hominoids/SBC_Case_Builder/mod/case_rack.scad

/*
    This file is part of SBC Case Builder https://github.com/hominoids/SBC_Case_Builder
    Copyright 2025 Edward A. Kisiel hominoid@cablemi.com

    This program is free software: you can redistribute it and/or modify
    it under the terms of the GNU General Public License as published by
    the Free Software Foundation, either version 3 of the License, or
    (at your option) any later version.

    but WITHOUT ANY WARRANTY; without even the implied warranty of
    MERCHANTABILITY or FITNESS FOR A PARTICULAR PURPOSE.  See the
    GNU General Public License for more details.

    You should have received a copy of the GNU General Public License
    along with this program.  If not, see <http://www.gnu.org/licenses/>
    Code released under GPLv3: http://www.gnu.org/licenses/gpl.html

    case_rack(case_design,side)


           NAME: case_rack
    DESCRIPTION: creates 1u-2u rack cases
           TODO: none

          USAGE: case_rack(case_design,side)

*/

module case_rack(case_design,side) {

rack_asm_gap = .25;
rack_asm_size = 5;
rack_asm_hole = 2.25;

if(case_design == "rack" && side == "bottom") {
    difference() {
        union() {
            difference() {
                union() {
                    difference() {
                        translate([(width/2)-wallthick-gap,(depth/2)-wallthick-gap,(case_z-floorthick)/2]) 
                            cube_fillet_inside([width,depth,case_z-floorthick], 
                                vertical=[corner_fillet,corner_fillet,0,0], 
                                    top=[0,0,0,0], bottom=[edge_fillet,edge_fillet,edge_fillet,edge_fillet,edge_fillet], $fn=90);
                        translate([(width/2)-wallthick-gap,(depth/2)-wallthick-gap,floorthick+(floorthick+case_z)/2]) 
                            cube_fillet_inside([width-(wallthick*2),depth-(wallthick*2),case_z+floorthick], 
                                    vertical=[corner_fillet-wallthick,corner_fillet-wallthick,-wallthick,-wallthick],
                                        top=[0,0,0,0], bottom=[edge_fillet,edge_fillet,edge_fillet,edge_fillet,edge_fillet], $fn=90);
                        // case upper panel clamp holes
                        translate([150-gap-wallthick,-gap-adj,case_z-13+4]) 
                            panel_clamp("rear", "sloped", "m2", 6, 18, 5, [true,10,2,"default"]);
                        translate([150-gap-wallthick,depth-gap-(2*wallthick)+adj,
                            case_z-13+4]) panel_clamp("front", "sloped", "m2", 6, 18, 5, [true,10,2,"default"]);
                        if(rack_width == 19) { 
                            translate([300-gap-wallthick,-gap-adj,case_z-13+4]) 
                                panel_clamp("rear", "sloped", "m2", 6, 18, 5, [true,10,2,"default"]);
                            translate([300-gap-wallthick,depth-gap-(2*wallthick)+adj,
                                case_z-13+4]) panel_clamp("front", "sloped", "m2", 6, 18, 5, [true,10,2,"default"]);
                        }

                    }
                    // rack mounting tabs
                    translate([-gap-wallthick, -gap+(sidethick-wallthick), 0]) 
                        rack_end_bracket("left", rack_size, sidethick);
                    translate([width-wallthick-gap, -gap+(sidethick-wallthick), 0]) 
                        rack_end_bracket("right", rack_size, sidethick);

                    // bay divider walls
                    for(r = [0:len(rack_bay_sbc)-1]) {
                        if(rack_bay_wall[r] == true) {
                            translate([-gap-wallthick-1+rack_asm_gap/2+75*(r+1),-gap-wallthick-adj,0]) 
                                cube([2,depth,case_z-floorthick-2]);
                        }
                    }
                    // case upper panel clamps
                    translate([150-gap-wallthick,-gap-adj,case_z-13+4]) 
                        panel_clamp("rear", "sloped", "m2", 6, 18, 5, [false,10,2,"default"]);
                    translate([150-gap-wallthick,depth-gap-(2*wallthick)+adj,
                        case_z-13+4]) panel_clamp("front", "sloped", "m2", 6, 18, 5, [false,10,2,"default"]);
                    if(rack_width == 19) { 
                        translate([300-gap-wallthick,depth-gap-(2*wallthick)+adj,
                            case_z-13+4]) panel_clamp("front", "sloped", "m2", 6, 18, 5, [false,10,2,"default"]);
                        translate([300-gap-wallthick,-gap-adj,case_z-13+4]) 
                            panel_clamp("rear", "sloped", "m2", 6, 18, 5, [false,10,2,"default"]);
                    }

                    // case floor panel clamps
                    translate([150-gap-wallthick,(depth/2)-gap-wallthick,floorthick-adj-.5]) 
                        panel_clamp("bottom", "sloped", "m2", 6, 18, 5, [false,10,2,"default"]);
                    if(rack_width == 19) { 
                        translate([300-gap-wallthick,(depth/2)-gap-wallthick,floorthick-adj-.5]) 
                            panel_clamp("bottom", "sloped", "m2", 6, 18, 5, [false,10,2,"default"]);
                    }
                    // top support
                    translate([-gap,depth-gap-wallthick-18,case_z-floorthick]) rotate([0,0,270])
                        panel_clamp("rear", "sloped", "m2", 6, 18, 5, [false,10,2,"default"]);
                    translate([width-gap-(2*wallthick),depth-gap-wallthick-18,case_z-floorthick])  rotate([0,0,270])
                        panel_clamp("front", "sloped", "m2", 6, 18, 5, [false,10,2,"default"]);
    
                    translate([-gap,18-gap,case_z-floorthick]) rotate([0,0,270])
                        panel_clamp("rear", "sloped", "m2", 6, 18, 5, [false,10,2,"default"]);
                    translate([width-gap-(2*wallthick),18-gap,case_z-floorthick])  rotate([0,0,270])
                        panel_clamp("front", "sloped", "m2", 6, 18, 5, [false,10,2,"default"]);
    
                    // additive accessories
                    if(accessory_name != "none") {
                        for (i=[1:11:len(accessory_data[a[0]])-1]) {
                            class = accessory_data[a[0]][i];
                            type = accessory_data[a[0]][i+1];
                            loc_x = accessory_data[a[0]][i+2];
                            loc_y = accessory_data[a[0]][i+3];
                            loc_z = accessory_data[a[0]][i+4];
                            face = accessory_data[a[0]][i+5];
                            rotation = accessory_data[a[0]][i+6];
                            parametric = accessory_data[a[0]][i+7];
                            size = accessory_data[a[0]][i+8];
                            data = accessory_data[a[0]][i+9];
                            mask = accessory_data[a[0]][i+10];

                            if(class == "add1" && face == "bottom") {
                                parametric_move_add(type, loc_x, loc_y, loc_z, face, rotation, parametric, 
                                    size, data, [false,mask[1],mask[2],mask[3]]);
                            }
                        }
                    }
                }
                // pcb and multi-pcb standoff holes 
                for(r = [0:len(rack_bay_sbc)-1]) {
                    if(rack_bay_sbc[r] != "none" && rack_bay_face[r] != "removable") {
                        s = search([rack_bay_sbc[r]],sbc_data);
                        pcb_id = sbc_data[s[0]][4];
                        pcb_width = sbc_data[s[0]][10][0];
                        pcb_depth = sbc_data[s[0]][10][1];
                        pcb_z_orig = sbc_data[s[0]][10][2];
                        pcb_tmaxz = sbc_data[s[0]][11][5];
                        pcb_bmaxz = sbc_data[s[0]][11][6];
                        pcb_color = sbc_data[s[0]][11][1];
                        pcb_radius = sbc_data[s[0]][11][0];

                        pcb_loc_x = rack_bay_rotation[r] == 90 ? rack_bay_xyz_loc[r][0] + pcb_width : 
                            rack_bay_rotation[r] == 180 ? rack_bay_xyz_loc[r][0] + pcb_width : rack_bay_xyz_loc[r][0];
                        pcb_loc_y = rack_bay_rotation[r] == 270 ? rack_bay_xyz_loc[r][1]+pcb_width : 
                            rack_bay_rotation[r] == 180 ? rack_bay_xyz_loc[r][1]+pcb_depth : rack_bay_xyz_loc[r][1];

                        translate([pcb_loc_x,pcb_loc_y,0]) rotate([0,0,rack_bay_rotation[r]]) union() {
                            // pcb standoff holes
                            if(sbc_bottom_standoffs == true) {
                                for (i=[1:11:len(sbc_data[s[0]])-2]) {
                                    class = sbc_data[s[0]][i+1];
                                    type = sbc_data[s[0]][i+2];
                                    id = sbc_data[s[0]][i+3];
                                    pcbhole_x = sbc_data[s[0]][i+4];
                                    pcbhole_y = sbc_data[s[0]][i+5];
                                    pcbhole_z = sbc_data[s[0]][i+6];
                                    pcbhole_size = sbc_data[s[0]][i+9][0];
                                    pcbhole_pos = sbc_data[s[0]][i+10][4];

                                    if (class == "pcbhole" && id == 0 && pcbhole_pos == "left_rear" && 
                                        bottom_rear_left_enable == true && bottom_standoff[6] != "blind") {
                                        ahpx = rack_bay_sbc[r] == "n2" ? 7 : rack_bay_sbc[r] == "n2+" ? 9.25 : 
                                            rack_bay_sbc[r] == "m1" ? 9.25 : pcbhole_x; 
                                        ahpy = rack_bay_sbc[r] == "n2" ? 15 : rack_bay_sbc[r] == "n2+" ? 9.25 : 
                                            rack_bay_sbc[r] == "m1" ? 9.25 : pcbhole_y; 
                                        translate([ahpx,ahpy,-adj]) 
                                            cylinder(d=bottom_standoff[4]-.2, h=floorthick+(2*adj));
                                    }
                                    if (class == "pcbhole" && id == 0 && pcbhole_pos == "left_front" && 
                                        bottom_front_left_enable == true && bottom_standoff[6] != "blind") {
                                        ahpx = rack_bay_sbc[r] == "n2" ? 8 : rack_bay_sbc[r] == "n2+" ? 9.25 : 
                                            rack_bay_sbc[r] == "m1" ? 9.25 : pcbhole_x; 
                                        ahpy = rack_bay_sbc[r] == "n2" ? 75 : rack_bay_sbc[r] == "n2+" ? 80.75 : 
                                            rack_bay_sbc[r] == "m1" ? 112.75 : pcbhole_y; 
                                        translate([ahpx,ahpy,-adj]) 
                                            cylinder(d=bottom_standoff[4]-.2, h=floorthick+(2*adj));
                                    }
                                    if (class == "pcbhole" && id == 0 && pcbhole_pos == "right_rear" && 
                                        bottom_rear_right_enable == true && bottom_standoff[6] != "blind") {
                                        ahpx = rack_bay_sbc[r] == "n2" ? 82 : rack_bay_sbc[r] == "n2+" ? 80.75 : 
                                            rack_bay_sbc[r] == "m1" ? 80.75 : pcbhole_x; 
                                        ahpy = rack_bay_sbc[r] == "n2" ? 6 : rack_bay_sbc[r] == "n2+" ? 9.25 : 
                                            rack_bay_sbc[r] == "m1" ? 9.25 : pcbhole_y; 
                                        translate([ahpx,ahpy,-adj]) 
                                            cylinder(d=bottom_standoff[4]-.2, h=floorthick+(2*adj));
                                    }
                                    if (class == "pcbhole" && id == 0 && pcbhole_pos == "right_front" && 
                                        bottom_front_right_enable == true && bottom_standoff[6] != "blind") {
                                        ahpx = rack_bay_sbc[r] == "n2" ? 82 : rack_bay_sbc[r] == "n2+" ? 80.75 : 
                                            rack_bay_sbc[r] == "m1" ? 80.75 : pcbhole_x; 
                                        ahpy = rack_bay_sbc[r] == "n2" ? 75 : rack_bay_sbc[r] == "n2+" ? 80.75 : 
                                            rack_bay_sbc[r] == "m1" ? 112.75 : pcbhole_y; 
                                        translate([ahpx,ahpy,-adj]) 
                                                cylinder(d=bottom_standoff[4]-.2, h=floorthick+(2*adj));
                                    }
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
