hominoids/SBC_Case_Builder/mod/case_side.scad

/*
    This file is part of SBC Case Builder https://github.com/hominoids/SBC_Case_Builder
    Copyright 2022,2023,2024 Edward A. Kisiel hominoid@cablemi.com

    This program is free software: you can redistribute it and/or modify
    it under the terms of the GNU General Public License as published by
    the Free Software Foundation, either version 3 of the License, or
    (at your option) any later version.

    but WITHOUT ANY WARRANTY; without even the implied warranty of
    MERCHANTABILITY or FITNESS FOR A PARTICULAR PURPOSE.  See the
    GNU General Public License for more details.

    You should have received a copy of the GNU General Public License
    along with this program.  If not, see <http://www.gnu.org/licenses/>
    Code released under GPLv3: http://www.gnu.org/licenses/gpl.html


           NAME: case_side
    DESCRIPTION: creates case side for supported designs and styles
           TODO: none

          USAGE: case_side(case_design, side)

*/

module case_side(case_design, side) {
    
    difference() {
        union() {
            if(case_design == "panel") {
                if(side == "rear") {
                    difference() {
                        union() {
                            translate([-gap,-wallthick-gap,-floorthick]) 
                                cube([width-2*wallthick,wallthick,case_z+2*floorthick]);
                            // right hook
                            difference() {
                                translate([width-(2*wallthick)-gap-adj,-wallthick-gap,
                                    ((case_z)/2)-4]) 
                                        cube([(2*wallthick)+.5,wallthick,8]);
                                translate([width-(2*wallthick)-gap-adj,-wallthick-gap-adj,
                                    ((case_z)/2)-4-adj]) 
                                        cube([wallthick+.25,wallthick+(2*adj),4.25]);
                            }
                            // left hook
                            difference() {
                                translate([-(2*wallthick)-gap-adj-.25,-wallthick-gap,
                                    ((case_z)/2)-4]) 
                                        cube([(2*wallthick)+.5,wallthick,8]);
                                translate([-wallthick-gap-adj-.25,-wallthick-gap-adj,
                                    ((case_z)/2)-4-adj]) 
                                        cube([wallthick+.25,wallthick+(2*adj),4.25]);
                            }
                        }
                        // top slots
                        translate([(width*(1/5))-8.25-(wallthick+gap),-wallthick-gap-adj,
                            case_z-floorthick-.25])
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
